ggajoch/power-meter-9000/esphome/components/bl0939addr/bl0939.h

#pragma once

#include "esphome/core/component.h"
#include "esphome/components/uart/uart.h"
#include "esphome/components/sensor/sensor.h"
#include "cf_delta.h"

namespace esphome {
namespace bl0939 {

struct ube24_t {  // NOLINT(readability-identifier-naming,altera-struct-pack-align)
  uint8_t l;
  uint8_t m;
  uint8_t h;
} __attribute__((packed));

struct ube16_t {  // NOLINT(readability-identifier-naming,altera-struct-pack-align)
  uint8_t l;
  uint8_t h;
} __attribute__((packed));

struct sbe24_t {  // NOLINT(readability-identifier-naming,altera-struct-pack-align)
  uint8_t l;
  uint8_t m;
  int8_t h;
} __attribute__((packed));

// Caveat: All these values are big endian (low - middle - high)

union DataPacket {  // NOLINT(altera-struct-pack-align)
  uint8_t raw[35];
  struct {
    uint8_t frame_header;  // 0x55 according to docs
    ube24_t ia_fast_rms;
    ube24_t ia_rms;
    ube24_t ib_rms;
    ube24_t v_rms;
    ube24_t ib_fast_rms;
    sbe24_t a_watt;
    sbe24_t b_watt;
    ube24_t cfa_cnt;
    ube24_t cfb_cnt;
    ube16_t tps1;
    uint8_t RESERVED1;  // value of 0x00
    ube16_t tps2;
    uint8_t RESERVED2;  // value of 0x00
    uint8_t checksum;   // checksum
  };
} __attribute__((packed));

class BL0939 : public PollingComponent, public uart::UARTDevice {
 public:
  void set_voltage_sensor(sensor::Sensor *voltage_sensor) { voltage_sensor_ = voltage_sensor; }
  void set_current_sensor_1(sensor::Sensor *current_sensor_1) { current_sensor_1_ = current_sensor_1; }
  void set_current_sensor_2(sensor::Sensor *current_sensor_2) { current_sensor_2_ = current_sensor_2; }
  void set_power_sensor_1(sensor::Sensor *power_sensor_1) { power_sensor_1_ = power_sensor_1; }
  void set_power_sensor_2(sensor::Sensor *power_sensor_2) { power_sensor_2_ = power_sensor_2; }
  void set_energy_sensor_1(sensor::Sensor *energy_sensor_1) { energy_sensor_1_ = energy_sensor_1; }
  void set_energy_sensor_2(sensor::Sensor *energy_sensor_2) { energy_sensor_2_ = energy_sensor_2; }
  void set_energy_sensor_sum(sensor::Sensor *energy_sensor_sum) { energy_sensor_sum_ = energy_sensor_sum; }
  void set_address(uint8_t address) { address_ = address; }
  void set_current_reference(float current_reference) { current_reference_ = current_reference; }
  void set_voltage_reference(float voltage_reference) { voltage_reference_ = voltage_reference; }
  void set_power_reference(float power_reference) { power_reference_ = power_reference; }
  void set_energy_reference(float energy_reference) { energy_reference_ = energy_reference; }
  void set_max_power(float max_power) { max_power_ = max_power; }

  void loop() override;

  void update() override;
  void setup() override;
  void dump_config() override;

//  protected:
  sensor::Sensor *voltage_sensor_{nullptr};
  sensor::Sensor *current_sensor_1_{nullptr};
  sensor::Sensor *current_sensor_2_{nullptr};
  // NB This may be negative as the circuits is seemingly able to measure
  // power in both directions
  sensor::Sensor *power_sensor_1_{nullptr};
  sensor::Sensor *power_sensor_2_{nullptr};
  sensor::Sensor *energy_sensor_1_{nullptr};
  sensor::Sensor *energy_sensor_2_{nullptr};
  sensor::Sensor *energy_sensor_sum_{nullptr};
  uint8_t address_{0};

  // Divide by this to turn into Ampere
  float current_reference_{0.0f};
  // Divide by this to turn into Volt
  float voltage_reference_{0.0f};
  // Divide by this to turn into Watt
  float power_reference_{0.0f};
  // Divide by this to turn into kWh
  float energy_reference_{0.0f};
  // Max plausible power per channel [W]; a bigger jump of CF_CNT means the chip reset its counter
  float max_power_{10000.0f};

  // CF_CNT is 24-bit and wraps at 2^24 (1702 kWh at the default energy_reference),
  // so energy is accumulated here from signed deltas. The chip keeps counting across a
  // SOFT_RESET, so a reboot takes a baseline from the first packet: energy restarts at 0,
  // same as after a power cycle.
  int64_t energy_pulses_[2]{0, 0};
  uint32_t last_cf_cnt_[2]{0, 0};
  uint32_t last_packet_ms_{0};
  bool have_baseline_{false};

  static uint32_t to_uint32_t(ube24_t input);

  static int32_t to_int32_t(sbe24_t input);

  bool validate_checksum(const DataPacket *data);

  void received_package_(const DataPacket *data);

  uint8_t write_command();

  uint8_t read_command();

  int time_update_start;
  bool needs_updating;
  bool waiting;
};
}  // namespace bl0939
}  // namespace esphome
